Ezekiel0108/Evereader/include/OxProto_Regular14pt7b.h

const uint8_t OxProto_Regular14pt7bBitmaps[] PROGMEM = {
  0x00, 0xF7, 0xBD, 0xEF, 0x39, 0xCE, 0x73, 0x9C, 0xE7, 0x00, 0x0E, 0xF7,
  0x9C, 0xE7, 0xF1, 0xF8, 0xFC, 0x66, 0x32, 0x19, 0x0C, 0x03, 0x1C, 0x0C,
  0x60, 0x71, 0x81, 0x8E, 0x3F, 0xFC, 0xFF, 0xF0, 0xE3, 0x03, 0x1C, 0x0C,
  0x70, 0x31, 0x81, 0xC6, 0x07, 0x38, 0x18, 0xE3, 0xFF, 0xEF, 0xFF, 0x8E,
  0x70, 0x31, 0xC0, 0xC6, 0x07, 0x18, 0x00, 0x03, 0x00, 0x0C, 0x00, 0x7C,
  0x0F, 0xFC, 0x7F, 0xF9, 0xCC, 0x66, 0x31, 0xD8, 0xC0, 0x73, 0x00, 0xFC,
  0x01, 0xF8, 0x00, 0xF8, 0x03, 0x78, 0x0C, 0x70, 0x31, 0xF8, 0xC7, 0x73,
  0x1D, 0xFF, 0xE1, 0xFF, 0x01, 0xF0, 0x03, 0x00, 0x0C, 0x00, 0x7C, 0x0D,
  0xFC, 0x33, 0x18, 0x66, 0x39, 0x8C, 0x77, 0x18, 0xCC, 0x3F, 0xB0, 0x3E,
  0x60, 0x01, 0x80, 0x06, 0x00, 0x0D, 0xE0, 0x37, 0xE0, 0xFC, 0xE1, 0xB0,
  0xC6, 0x61, 0x8C, 0xC3, 0x31, 0xCE, 0xC1, 0xF9, 0x81, 0xE0, 0x0F, 0xC0,
  0x3F, 0xC0, 0xF3, 0xC1, 0xC3, 0x83, 0x87, 0x07, 0x00, 0x07, 0x00, 0x06,
  0x00, 0x0E, 0x0E, 0x7E, 0x19, 0xEE, 0x33, 0x0E, 0xEE, 0x0F, 0x9C, 0x1F,
  0x38, 0x1E, 0x70, 0x3C, 0x78, 0xFC, 0x7F, 0xDC, 0x7E, 0x10, 0xFF, 0xFD,
  0x90, 0x00, 0x80, 0xC1, 0xE1, 0xE1, 0xE1, 0xE0, 0xE0, 0xE0, 0x70, 0x38,
  0x18, 0x1C, 0x0E, 0x07, 0x03, 0x80, 0xE0, 0x70, 0x38, 0x0E, 0x07, 0x81,
  0xE0, 0x78, 0x1E, 0x07, 0x00, 0x80, 0x40, 0x30, 0x3E, 0x0F, 0x81, 0xE0,
  0x70, 0x1C, 0x0E, 0x03, 0x81, 0xC0, 0xE0, 0x70, 0x18, 0x0C, 0x0E, 0x07,
  0x03, 0x83, 0x81, 0xC1, 0xC1, 0xE1, 0xE3, 0xE0, 0xC0, 0x40, 0x00, 0x07,
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
  {   947,  13,  19,  17,    2,  -18 },   // 0x46 'F'
  {   978,  15,  19,  17,    1,  -18 },   // 0x47 'G'
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

const GFXfont OxProto_Regular14pt7b PROGMEM = {
  (uint8_t  *)OxProto_Regular14pt7bBitmaps,
  (GFXglyph *)OxProto_Regular14pt7bGlyphs,
  0x20, 0x7E, 43 };

// Approx. 3279 bytes
